ccadic/LightningNetworkPCB/autonomous01.jpg

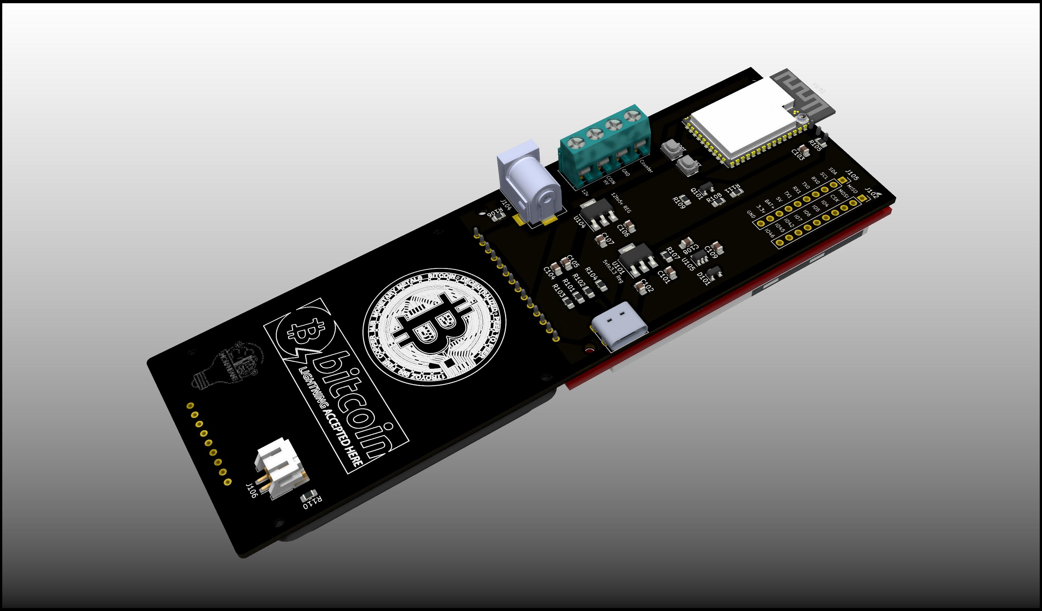
autonomous01.jpg
