ccadic/LightningNetworkPCB/autonomous5.jpg

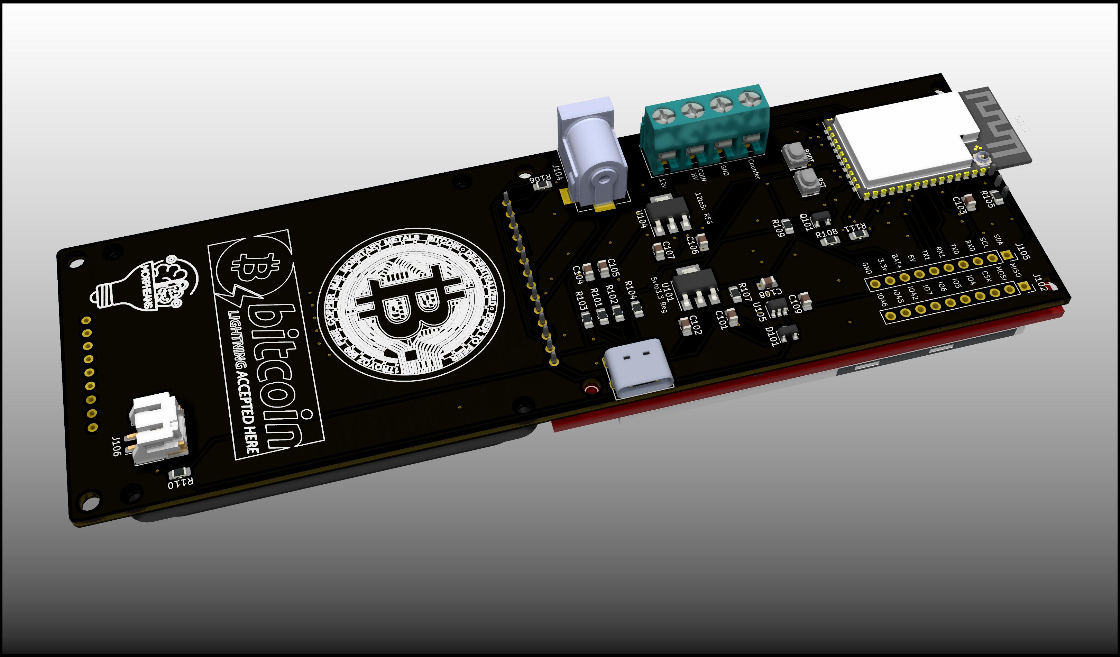
autonomous5.jpg
